alanb128/ultimate-noise-box/controller/assets/default.jpg

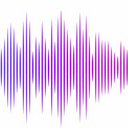
controller/assets/default.jpg
