alanb128/ultimate-noise-box/controller/assets/idle.jpg

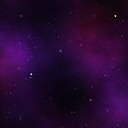
controller/assets/idle.jpg
