alanb128/ultimate-noise-box/noise/assets/brown_noise.jpg

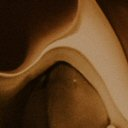
noise/assets/brown_noise.jpg
