alanb128/ultimate-noise-box/noise/assets/pink_noise.jpg

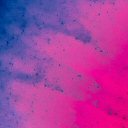
noise/assets/pink_noise.jpg
