alanb128/ultimate-noise-box/noise/assets/rain.jpg

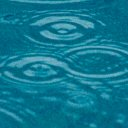
noise/assets/rain.jpg
