alanb128/ultimate-noise-box/noise/assets/underwater.jpg

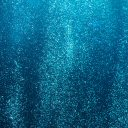
noise/assets/underwater.jpg
