alanb128/ultimate-noise-box/noise/assets/white_noise.jpg

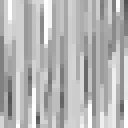
noise/assets/white_noise.jpg
